ywhs05/DigitalToFiberOpticConverter-PCB/DaFO-PCB/DaFO/3D models/SN74AHC1G14DBVR.step

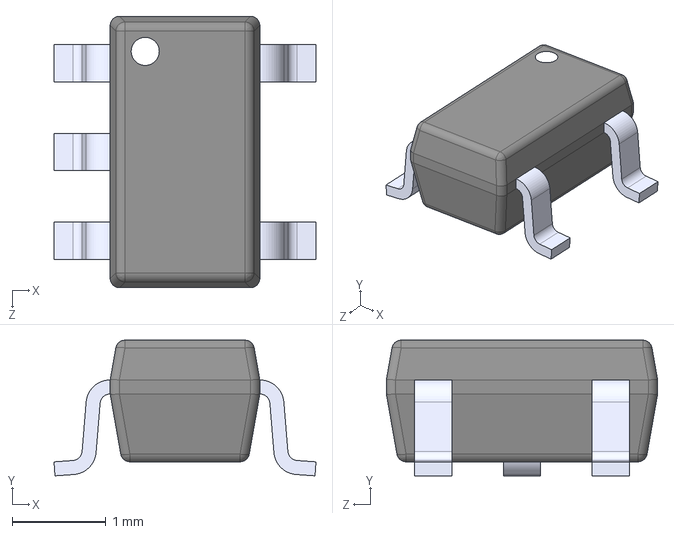
[picture p21: CAD file, 2026-02-09]
DaFO-PCB/DaFO/3D models/SN74AHC1G14DBVR.step
2.80 x 1.45 x 2.90 mm
