ywhs05/DigitalToFiberOpticConverter-PCB/DaFO-PCB/DaFO/3D models/BAS85_GS08.stp

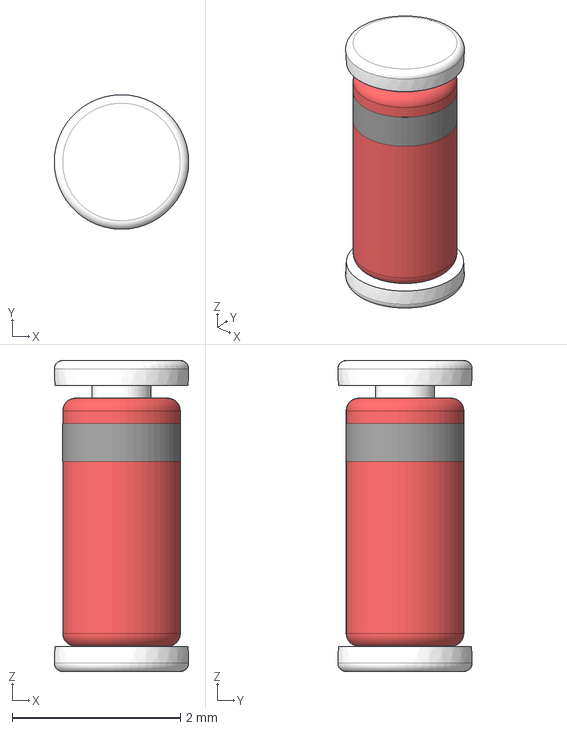
[picture p22: CAD file, 2026-02-09]
DaFO-PCB/DaFO/3D models/BAS85_GS08.stp
1.60 x 1.60 x 3.70 mm
