ywhs05/DigitalToFiberOpticConverter-PCB/DaFO-PCB/DaFO/3D models/CAP_X7R_0603_AVX.step

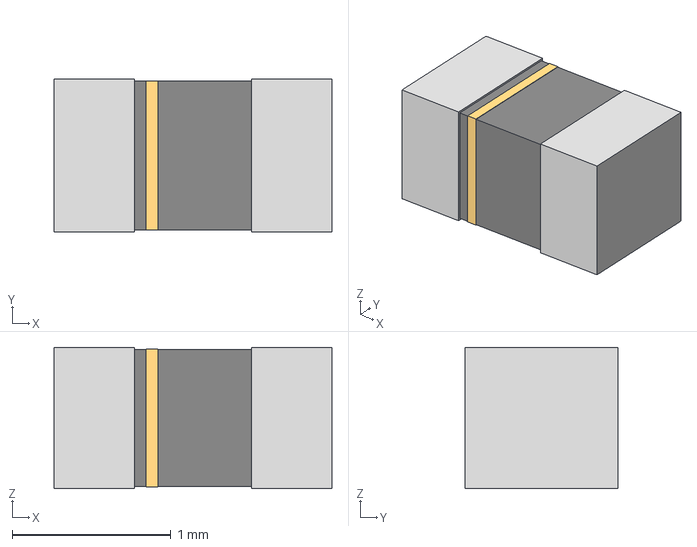
[picture p23: CAD file, 2026-02-09]
DaFO-PCB/DaFO/3D models/CAP_X7R_0603_AVX.step
1.75 x 0.966 x 0.889 mm
