ywhs05/DigitalToFiberOpticConverter-PCB/DaFO-PCB/DaFO/3D models/CON_PC_1935776.step

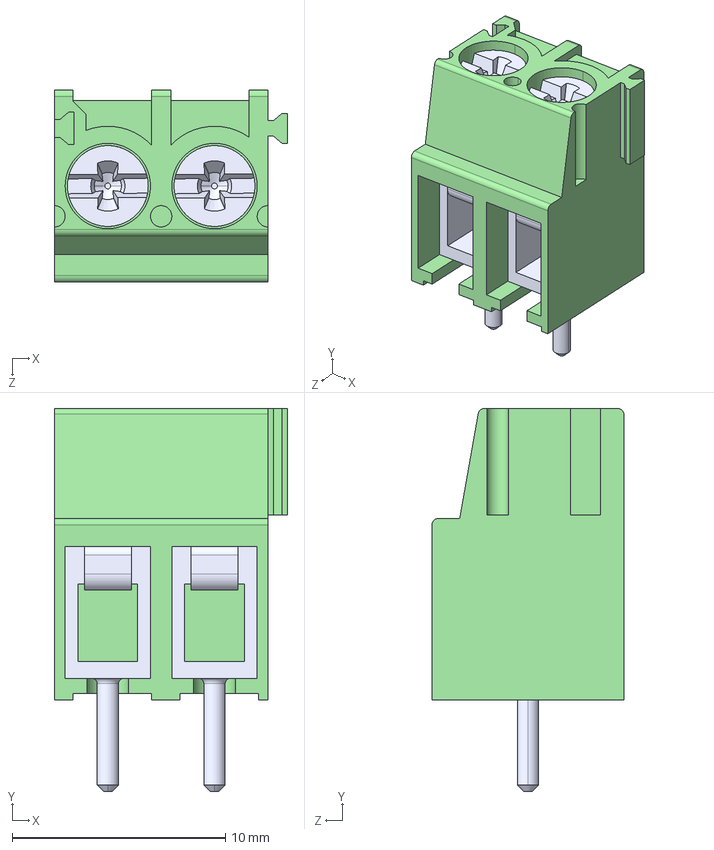
[picture p24: CAD file, 2026-02-09]
DaFO-PCB/DaFO/3D models/CON_PC_1935776.step
10.9 x 17.9 x 9.00 mm
